UdhayanDherman17/EEG-Movement-Imagery/ESP8266_Circuit/NodeMCU-Circuit.kicad_sch

## KiCad design ESP8266_Circuit/NodeMCU-Circuit.kicad_sch (2023-06-06)

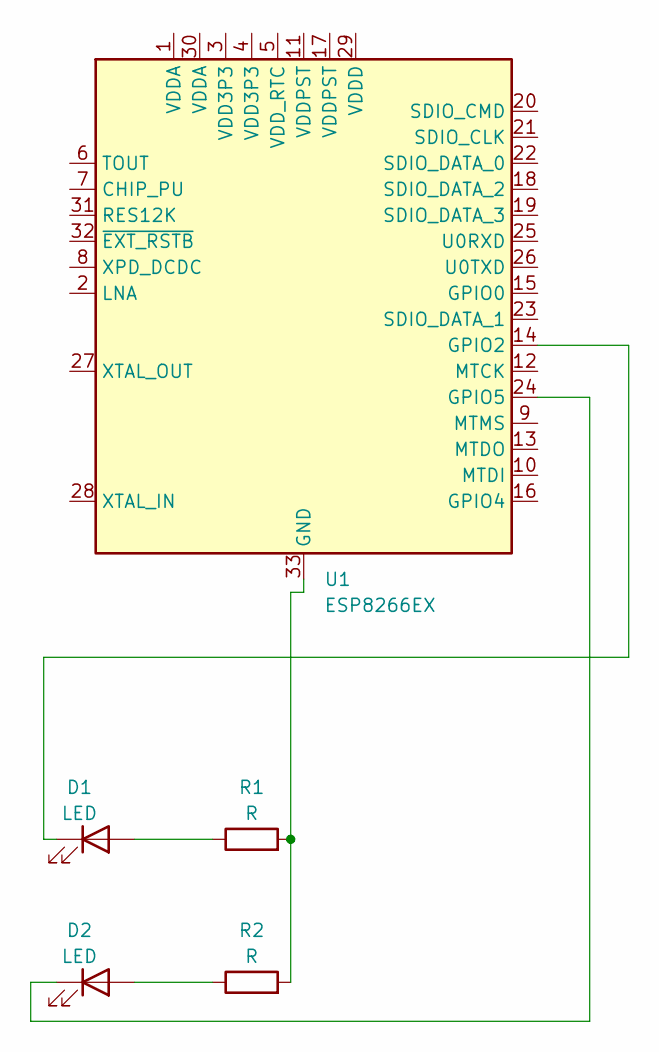
[picture p23: schematic NodeMCU-Circuit.kicad_sch]

Parts:
D1, D2: LED
R1, R2: R
U1: ESP8266EX; QFN-32-1EP_5x5mm_P0.5mm_EP3.45x3.45mm

Connections:
unnamed: D1.1 (K), U1.14 (GPIO2)
unnamed: D1.2 (A), R1.1
unnamed: D2.1 (K), U1.24 (GPIO5)
unnamed: D2.2 (A), R2.1
unnamed: R1.2, R2.2, U1.33 (GND)
